lamikr/i2s_to_toslink_pcb/factory/pcb/gerber/i2s_to_toslink_pcb-F_Cu.pdf

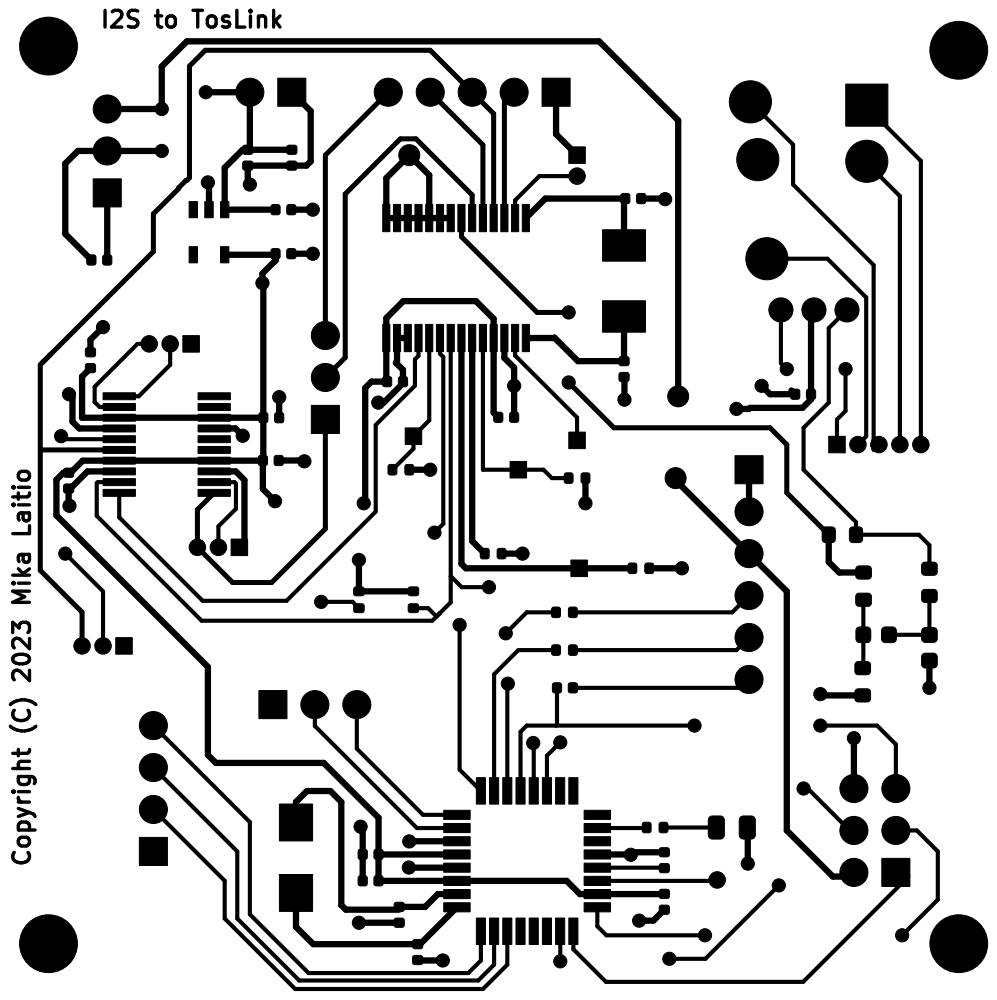
[picture p13: page 1]

I2S to TosLink Copyright (C) 2023 Mika Laitio
