lamikr/i2s_to_toslink_pcb/factory/pcb/gerber/i2s_to_toslink_pcb-F_Mask.pdf

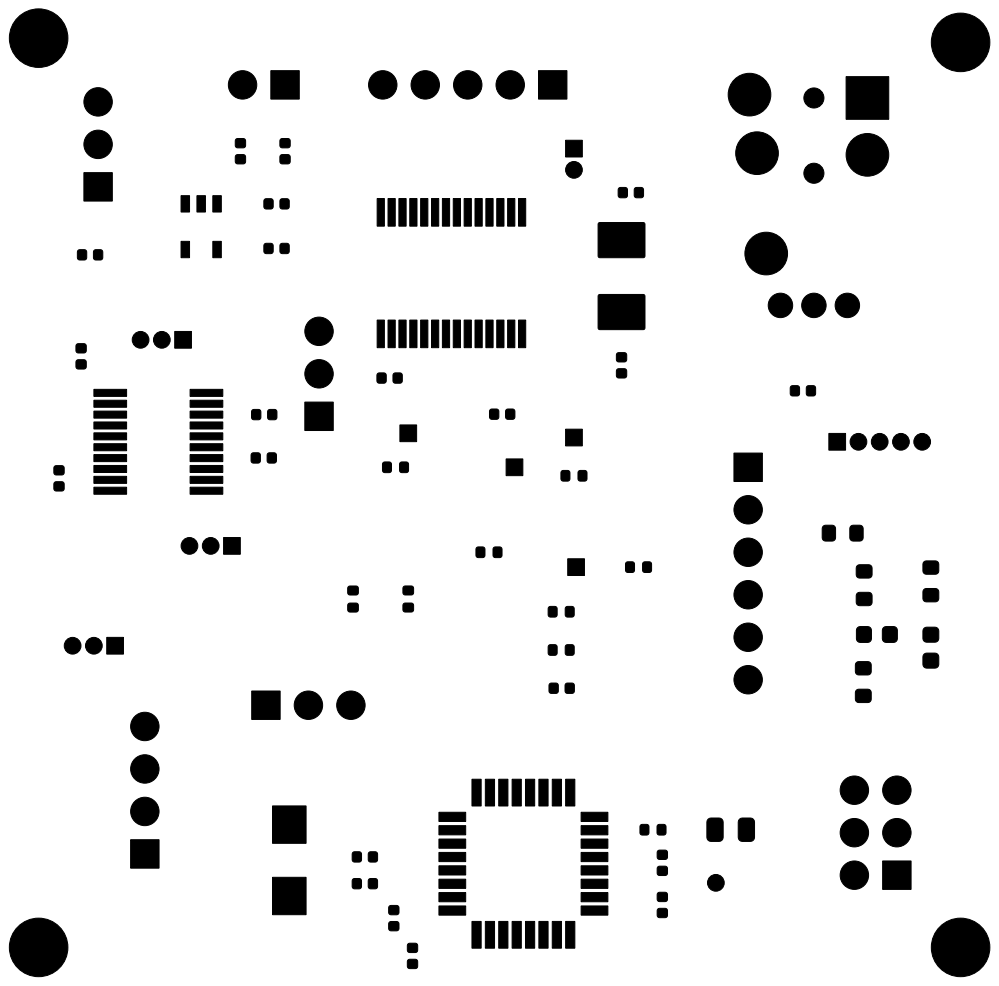
[picture p14: page 1]
