lamikr/i2s_to_toslink_pcb/factory/pcb/gerber/i2s_to_toslink_pcb-F_Paste.pdf

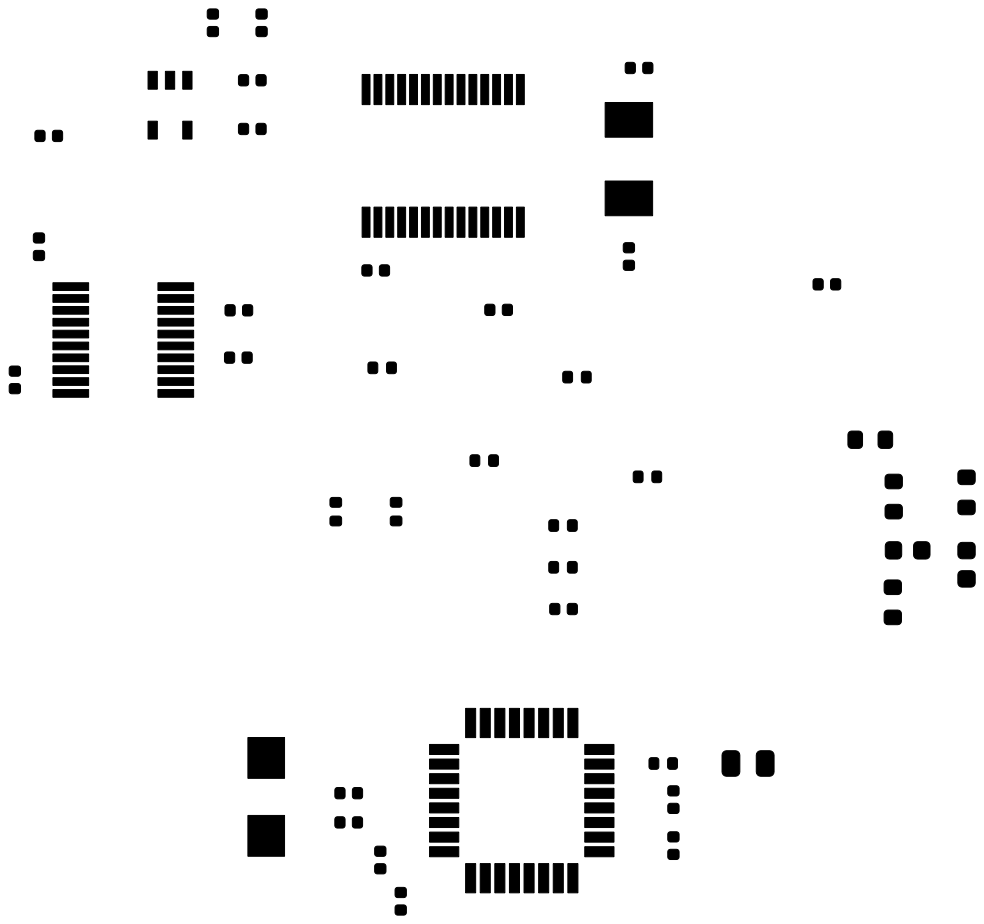
[picture p15: page 1]
