lamikr/i2s_to_toslink_pcb/factory/pcb/gerber/i2s_to_toslink_pcb-F_Silkscreen.pdf

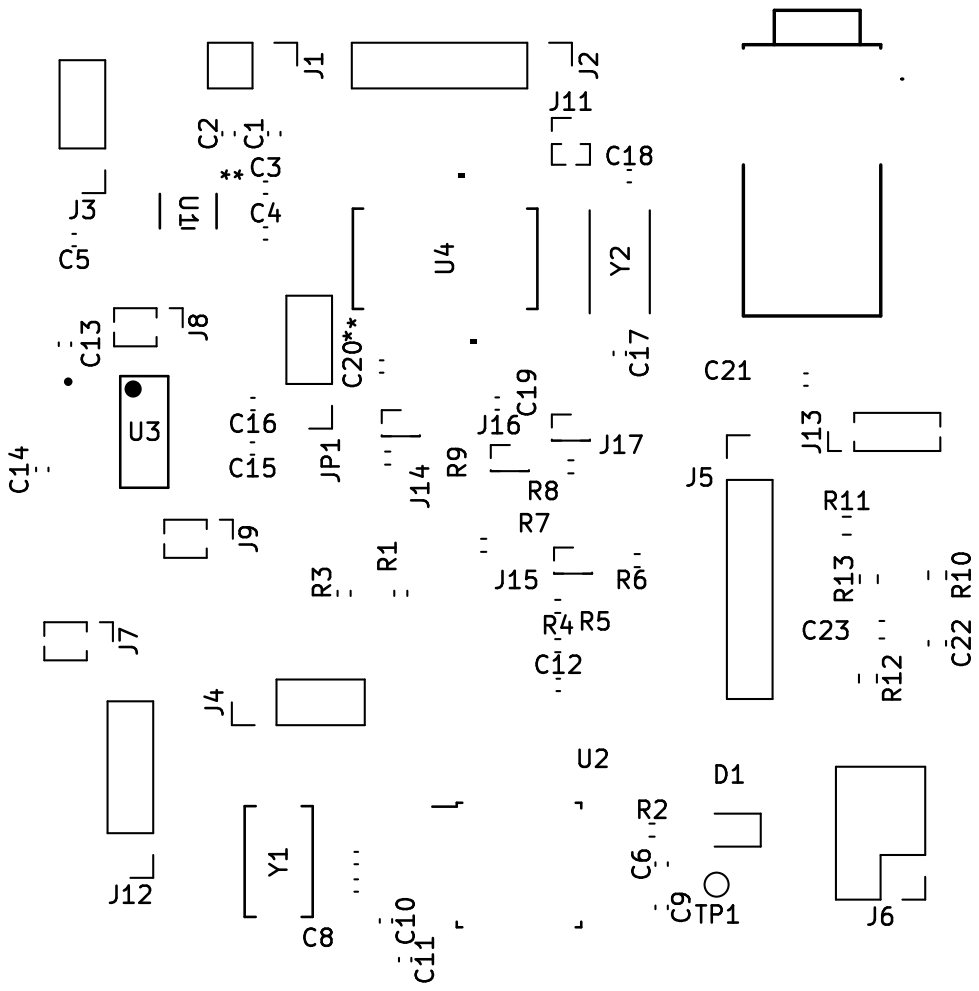
[picture p16: page 1]
